adamoell/LaserStramash/Software/Gun/game.py

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

########################################################################
# TODO State changes should be made by the Game calling player.up etc
# ALL network comms to be handled by the Game
# TODO Free-For-All Game class
########################################################################
        
class Hit:
    """
    Represents a hit
    """

    def __init__(self, shooterteam, shooter, victimteam, victim, sensor):
        self.shooterteam = shooterteam 
        self.shooter = shooter 
        self.victimteam = victimteam 
        self.victim = victim 
        self.sensor = sensor

    @property
    def message(self):
        # TODO: hits should really only ever be JSONified in the StramashClient
        """
        Returns the JSON for the hit
        """
        msg = "["+str(self.shooterteam)+","+str(self.shooter)+","+str(self.victimteam)+","+str(self.victim)+","+str(self.sensor)+"]"
        return msg

class Game:
    """
    Base class for implementing a Game. To create a specific Game, subclass this.
    """
    def __init__(self, stramash):
        """
        Initialises the game. Subclasses should invoke this via super().__init__()
        in order to get the networking etc hooked up.
        """
        # TODO: hookup callbacks to stramash
        # TODO: kick off a thread to sleep until game end, and then call the game end code

        pass 


    ############################################################################
    # Pre Game Start
    ############################################################################
    # TODO: stramash/player/<playerid>/gamejoined - create the appropriate Game
    # object
    # TODO: stramash/player/<playerid>/assigned
    # TODO: stramash/player/<playerid>/unassigned
    # TODO: stramash/player/<playerid>/deleted
    # TODO: stramash/player/<playerid>/kicked - NOT USED IN PROTO
    # TODO: stramash/player/<playerid>/up - NOT USED IN PROTO
    # TODO: stramash/player/<playerid>/down - NOT USED IN PROTO
    # TODO: stramash/game/<gameid>/gamestarted
    #       In proto, this will shut down network
    # TODO: stramash/game/<gameid>/gamedeleted
    # TODO: 


    ############################################################################
    # During Game Play
    ############################################################################
    
    
    # TODO: Hook hit/fire callbacks - post-prototype we will send:
    # - stramash/game/<gameid>/fire
    # - stramash/game/<gameid>/hit
    # TODO: handlers for in-game network server messages. NB: we are disabling 
    # network during gameplay in the prototype to improve IR accuracy
    # TODO: stramash/game/<gameid>/gameended - NOT USED IN PROTO
    

    ############################################################################
    # Post Game Finish
    ############################################################################
    # TODO: PROTO- gun must send stats on shots fired and hits to server, and 
    # go back to initial state.
    pass
