adamoell/LaserStramash/Software/Gun/wifi.py

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
# listen on pc:
# mosquitto_sub -h 192.168.1.2 -t dbg -t hit
from time import sleep 
import machine
import network
from utils import *

class WiFi:
    def __init__(self, ssid, key):
        self.ssid = ssid 
        self.key = key

    def connect(self):
        """
        Connect to the wifi access point
        """
        self.sta_if = network.WLAN(network.STA_IF)
        self.sta_if.active(False)
        sleep(1)
        self.sta_if.active(True)

        dbg("Interface active")
        if self.check_ap(self.ssid):
            # connect to access point
            if not self.sta_if.isconnected():
                dbg('connecting to AP...')
                self.sta_if.active(True)
                self.sta_if.connect(self.ssid, self.key)
                while not self.sta_if.isconnected():
                    machine.idle()
                    # Do we need a timeout here?
                dbg(self.sta_if.ifconfig())
            else:
                dbg("WLAN already connected")
                dbg(self.sta_if.ifconfig())
        else:
            dbg("Target SSID not found.")
            reset("Could not connect to network - target SSID is not availble.", HARD)
    
    def check_ap(self, targetssid):
        """
        Check if the given access point exists
        """
        dbg(f"Scanning for access point [{targetssid}]...")
        
        self.sta_if.active(True)
        networks = self.sta_if.scan()

        for ssid, bssid, channel, rssi, authmode, hidden in sorted(networks, key=lambda x: x[3], reverse=True):
            ssid = ssid.decode('utf-8')
            dbg(f"Found {ssid}")
            if ssid == targetssid:
                dbg("Found access point!")
                return True 
        
        dbg("Access point not found")
        return False
